tvv00000/Eriala-individuaalaine---Robootika-projekti-edasiarendus/hardware/lable cover 45.stl

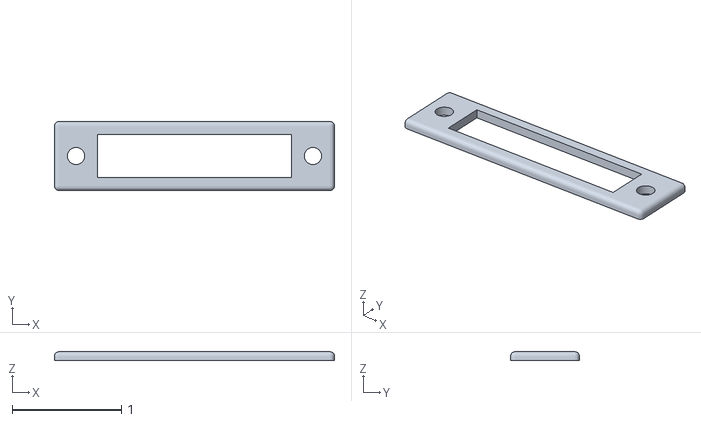
[picture p23: CAD file, 2026-06-19]
hardware/lable cover 45.stl
2.56 x 0.63 x 0.0787
