tvv00000/Eriala-individuaalaine---Robootika-projekti-edasiarendus/hardware/lable cover 35.stl

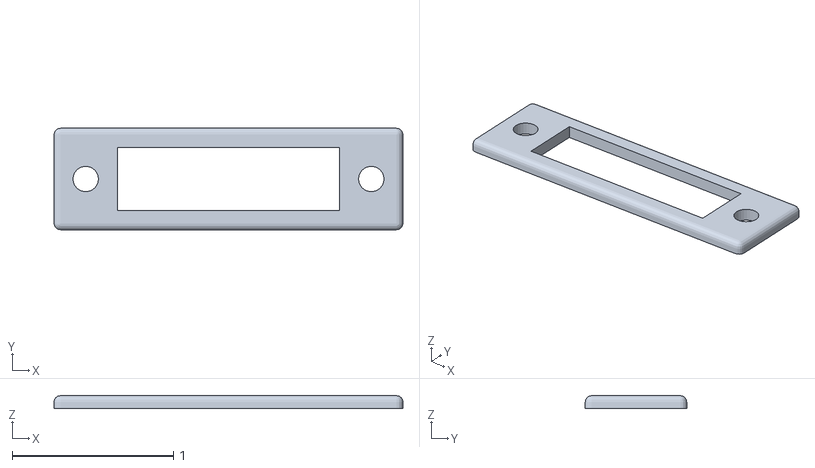
[picture p24: CAD file, 2026-06-19]
hardware/lable cover 35.stl
2.17 x 0.63 x 0.0787
