tvv00000/Eriala-individuaalaine---Robootika-projekti-edasiarendus/hardware/Turbine panel.stl

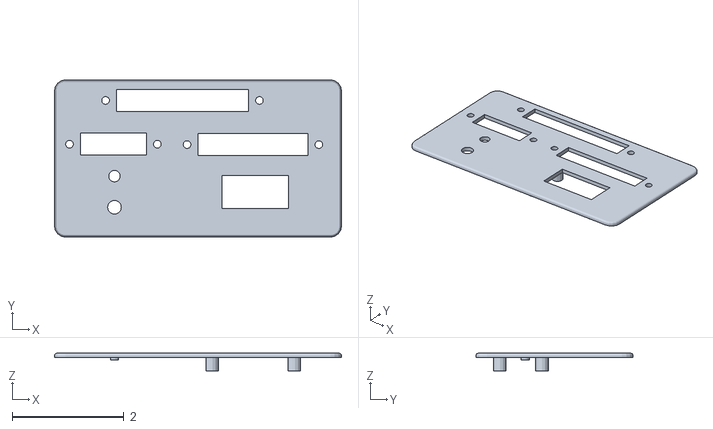
[picture p25: CAD file, 2026-06-19]
hardware/Turbine panel.stl
5.14 x 2.82 x 0.315
