tvv00000/Eriala-individuaalaine---Robootika-projekti-edasiarendus/hardware/LCD MOUNT.stl

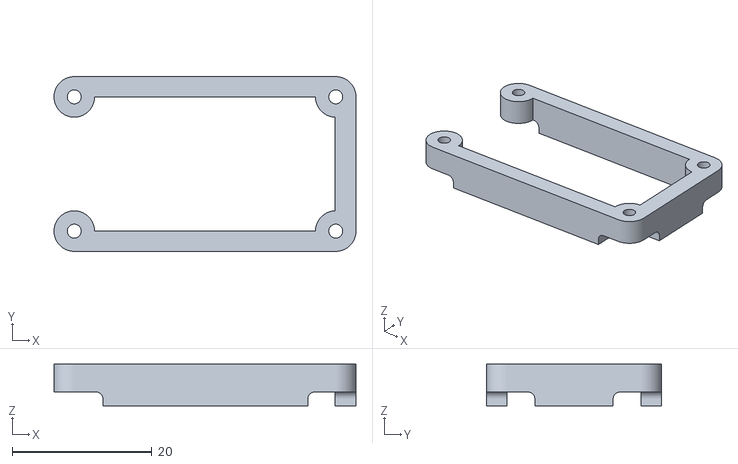
[picture p26: CAD file, 2026-06-19]
hardware/LCD MOUNT.stl
43.2 x 25.0 x 6.00
