tvv00000/Eriala-individuaalaine---Robootika-projekti-edasiarendus/hardware/STORAGE BOX.stl

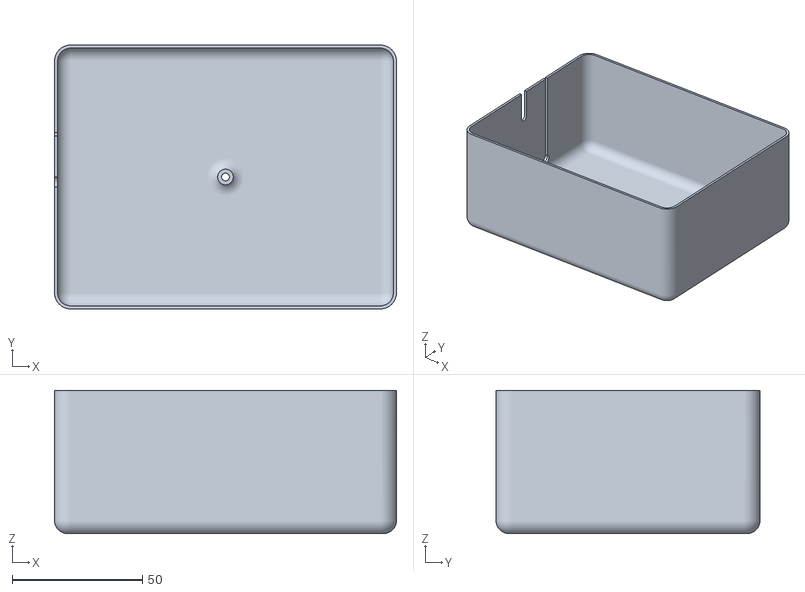
[picture p27: CAD file, 2026-06-19]
hardware/STORAGE BOX.stl
131.4 x 101.4 x 55.0
