tvv00000/Eriala-individuaalaine---Robootika-projekti-edasiarendus/hardware/STORAGE BOX top.stl

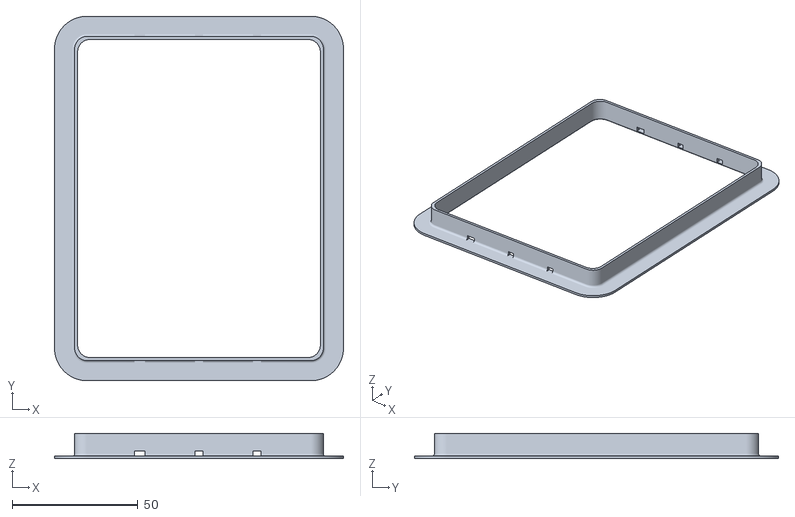
[picture p28: CAD file, 2026-06-19]
hardware/STORAGE BOX top.stl
114.9 x 144.9 x 10.0
