tvv00000/Eriala-individuaalaine---Robootika-projekti-edasiarendus/hardware/nameplate.stl

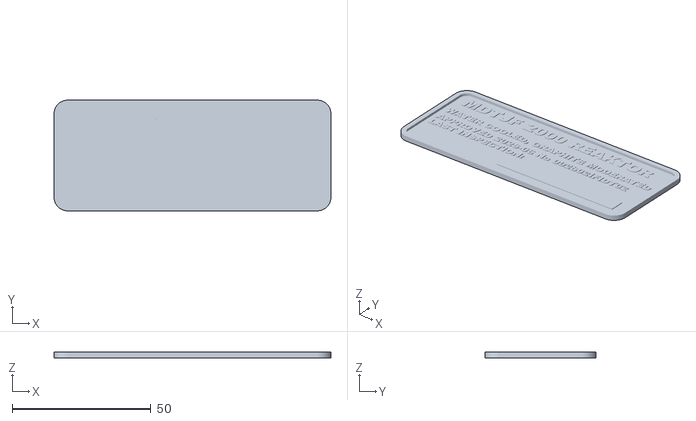
[picture p29: CAD file, 2026-06-19]
hardware/nameplate.stl
100.0 x 40.0 x 2.00
