tvv00000/Eriala-individuaalaine---Robootika-projekti-edasiarendus/hardware/pump paneel.stl

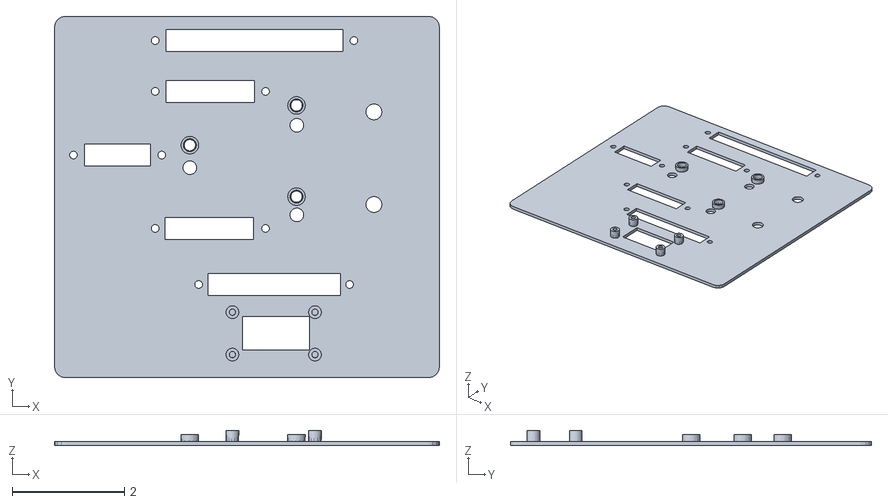
[picture p30: CAD file, 2026-06-19]
hardware/pump paneel.stl
6.87 x 6.45 x 0.276
