tvv00000/Eriala-individuaalaine---Robootika-projekti-edasiarendus/hardware/fuel control.stl

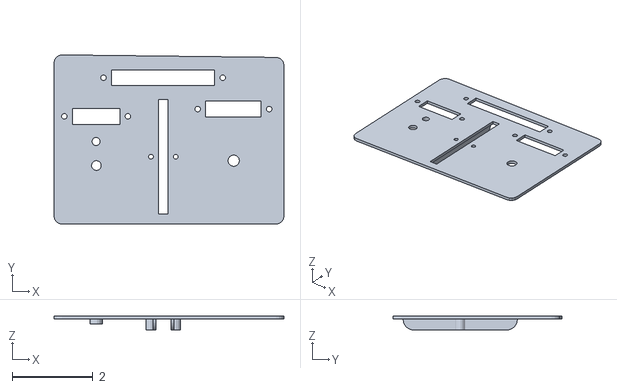
[picture p31: CAD file, 2026-06-19]
hardware/fuel control.stl
5.70 x 4.19 x 0.354
