tvv00000/Eriala-individuaalaine---Robootika-projekti-edasiarendus/hardware/slide pote bottom.stl

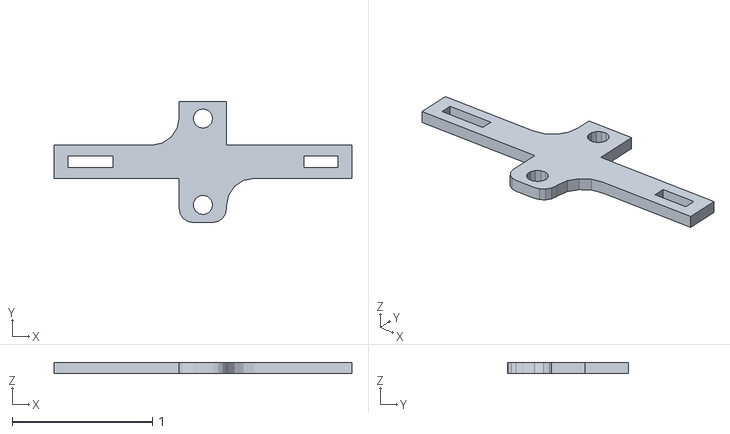
[picture p32: CAD file, 2026-06-19]
hardware/slide pote bottom.stl
2.13 x 0.864 x 0.0787
